busycircuits/alm014-fizzle-guts/firmware/uu.h

/*
*   'UU' - Small AVR utility lib
* 
*   Copyright (c) 2014 ALM Co Ltd
*
*   Parts of code based in Wiring/Arduino.h;
*   Copyright (c) 2005-2006 David A. Mellis
*   
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
*/

#ifndef _HAVE_UU_H
#define _HAVE_UU_H

#include <stdint.h>
#include <stdlib.h>

#include <avr/io.h>
#include <avr/pgmspace.h>
#include <util/delay.h>
#include <avr/eeprom.h>
#include <avr/interrupt.h>

/* Pin defs.. - FIXME: should enum this probably as a type... */

#define PIN_A0 0x0
#define PIN_A1 0x1
#define PIN_A2 0x2
#define PIN_A3 0x3
#define PIN_A4 0x4
#define PIN_A5 0x5
#define PIN_A6 0x6
#define PIN_A7 0x7
#define PIN_B0 0x10
#define PIN_B1 0x11
#define PIN_B2 0x12
#define PIN_B3 0x13
#define PIN_B4 0x14
#define PIN_B5 0x15
#define PIN_B6 0x16
#define PIN_B7 0x17
#define PIN_C0 0x20
#define PIN_C1 0x21
#define PIN_C2 0x22
#define PIN_C3 0x23
#define PIN_C4 0x24
#define PIN_C5 0x25
#define PIN_C6 0x26
#define PIN_C7 0x27
#define PIN_D0 0x30
#define PIN_D1 0x31
#define PIN_D2 0x32
#define PIN_D3 0x33
#define PIN_D4 0x34
#define PIN_D5 0x35
#define PIN_D6 0x36
#define PIN_D7 0x37
#define PIN_E0 0x40
#define PIN_E1 0x41
#define PIN_E2 0x42
#define PIN_E3 0x43
#define PIN_E4 0x44
#define PIN_E5 0x45
#define PIN_E6 0x46
#define PIN_E7 0x47

#define HIGH 0x1
#define LOW  0x0

#define INPUT 0x0
#define OUTPUT 0x1
#define INPUT_PULLUP 0x2

#define LSBFIRST 0
#define MSBFIRST 1

#ifndef _BV
#define _BV(n) (1<<(n))
#endif

#define TRUE  0x1
#define FALSE 0x0

#define PI 3.1415926535897932384626433832795
#define HALF_PI 1.5707963267948966192313216916398
#define TWO_PI 6.283185307179586476925286766559
#define DEG_TO_RAD 0.017453292519943295769236907684886
#define RAD_TO_DEG 57.295779513082320876798154814105

#define SERIAL  0x0
#define DISPLAY 0x1

#define LSBFIRST 0
#define MSBFIRST 1

#define CHANGE 1
#define FALLING 2
#define RISING 3

#define USART_BAUDRATE 9600
#define BAUD_PRESCALE (((F_CPU / (USART_BAUDRATE * 16UL))) - 1) 

#define MIN(a,b) ((a)<(b)?(a):(b))
#define MAX(a,b) ((a)>(b)?(a):(b))
#define ABS(x) ((x)>0?(x):-(x))
#define CONSTRAIN(amt,low,high) ((amt)<(low)?(low):((amt)>(high)?(high):(amt)))
#define ROUND(x)     ((x)>=0?(long)((x)+0.5):(long)((x)-0.5))
#define RADIANS(deg) ((deg)*DEG_TO_RAD)
#define DEGREES(rad) ((rad)*RAD_TO_DEG)
#define SQ(x) ((x)*(x))

extern const uint8_t PROGMEM digital_pin_table_PGM[];

#define PIN_TO_MASK(p)    (1<<(p & 0x0f))
#define PIN_TO_PORTREG(p) \
  ((volatile uint8_t *)((int)pgm_read_byte(_pin_table_PGM+(p>>4))))
#define PIN_TO_MODEREG(p) (PIN_TO_PORTREG(p) + 1)
#define PIN_TO_OUTREG(p) (PIN_TO_PORTREG(p) + 2) 

#define uu_bit_low_byte(w) ((uint8_t) ((w) & 0xff))
#define uu_bit_high_byte(w) ((uint8_t) ((w) >> 8))
#define uu_bit_read(value, bit) (((value) >> (bit)) & 0x01)
#define uu_bit_set(value, bit) ((value) |= (1UL << (bit)))
#define uu_bit_clear(value, bit) ((value) &= ~(1UL << (bit)))
#define uu_bit_write(value, bit, bitvalue) (bitvalue ? uu_bit_set(value, bit) : uu_bit_clear(value, bit))
#define uu_bit(b) (1UL << (b))
#define uu_bit_is_set(value,pos) ((value) & (1<<(pos)))

typedef unsigned int word;
typedef int bool;
typedef unsigned char Pin;
typedef unsigned char byte;

#define uu_interrupts_on() sei()
#define uu_interrupts_off() cli()

void
uu_usart_init();

void uu_usart_putc(char c);

void uu_usart_puts(char *s); 

/* via https://github.com/sultanqasim/Stellarino/blob/master/stellarino_uart.c */
void uu_usart_puti(long i);


void 
uu_delay_ms(uint16_t ms); 

void 
uu_delay_us(unsigned int us);

void 
uu_pin_mode (Pin pin, bool output);

void 
uu_pin_digital_write (Pin pin, bool value);

bool 
uu_pin_digital_read (Pin pin);

void 
uu_pin_shift_out(Pin dataPin, Pin clockPin, uint8_t bitOrder, uint8_t value);

uint8_t 
uu_pin_shift_in(Pin dataPin, Pin clockPin, uint8_t bitOrder);

void
uu_init(int flags);


#define B0 0
#define B00 0
#define B000 0
#define B0000 0
#define B00000 0
#define B000000 0
#define B0000000 0
#define B00000000 0
#define B1 1
#define B01 1
#define B001 1
#define B0001 1
#define B00001 1
#define B000001 1
#define B0000001 1
#define B00000001 1
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
#define B11110011 243
#define B11110100 244
#define B11110101 245
#define B11110110 246
#define B11110111 247
#define B11111000 248
#define B11111001 249
#define B11111010 250
#define B11111011 251
#define B11111100 252
#define B11111101 253
#define B11111110 254
#define B11111111 255

#endif
